Batterhead221/HIVE/Outputs/IMG/L1-SIG.png

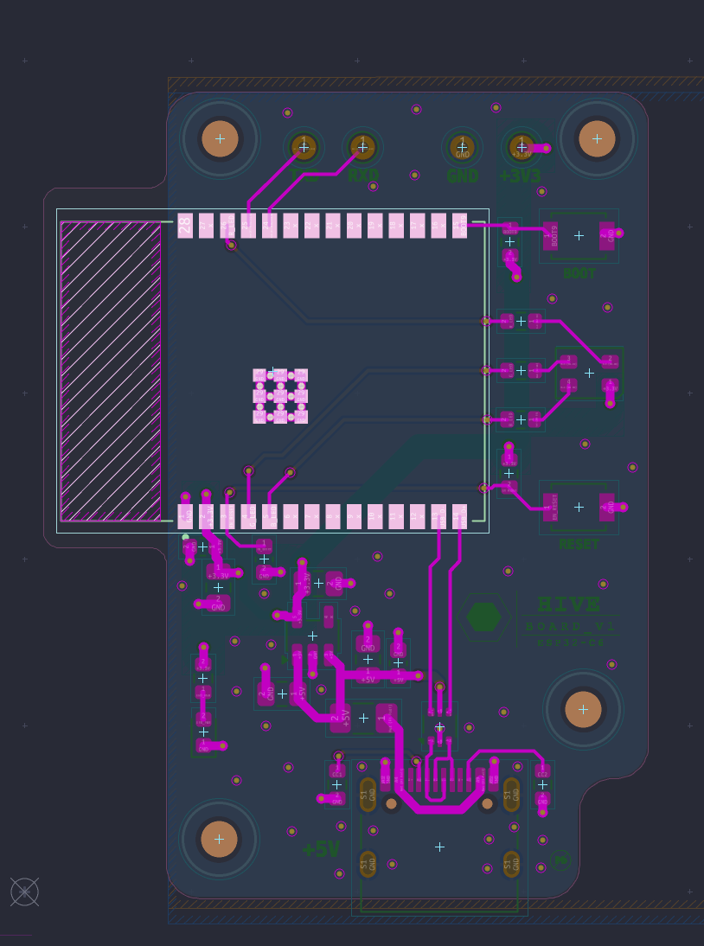
Outputs/IMG/L1-SIG.png
