Batterhead221/HIVE/Outputs/IMG/L2_GND.png

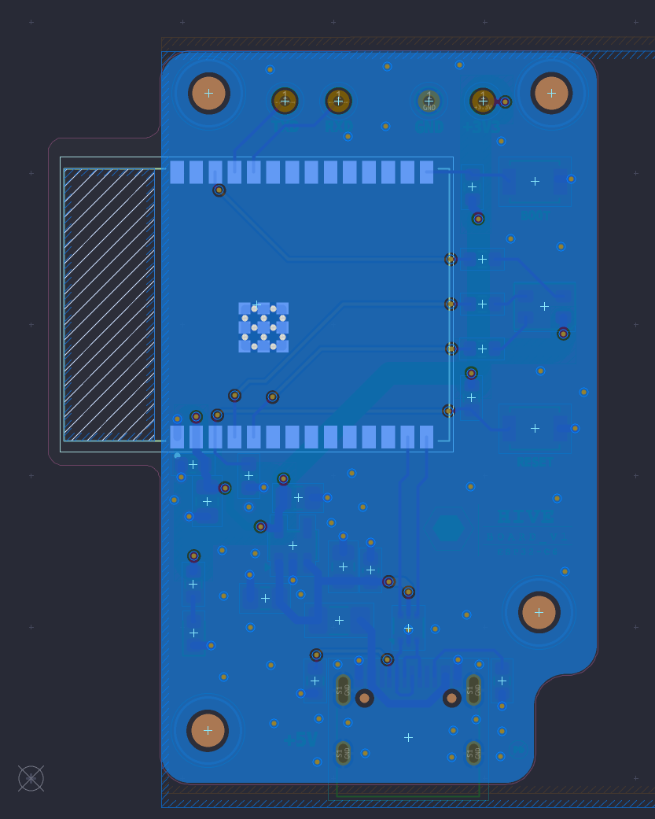
Outputs/IMG/L2_GND.png
