Batterhead221/HIVE/Outputs/IMG/L3-3V3.png

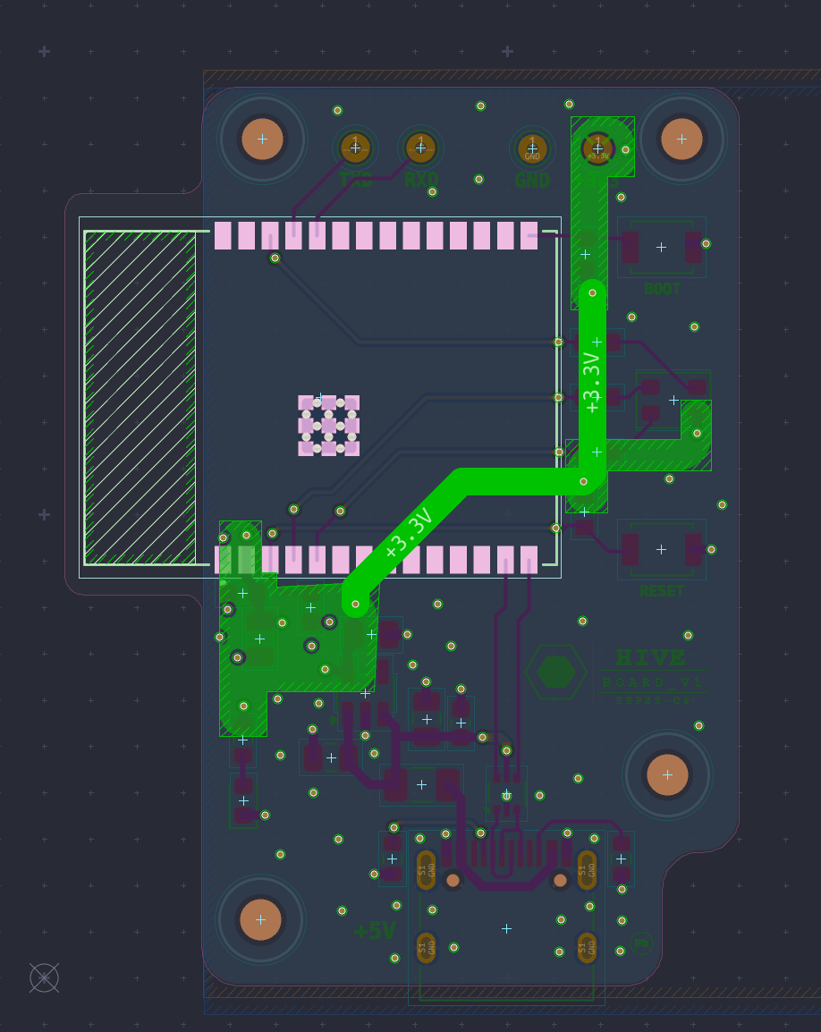
Outputs/IMG/L3-3V3.png
