Batterhead221/HIVE/Outputs/IMG/L4-MIX.png

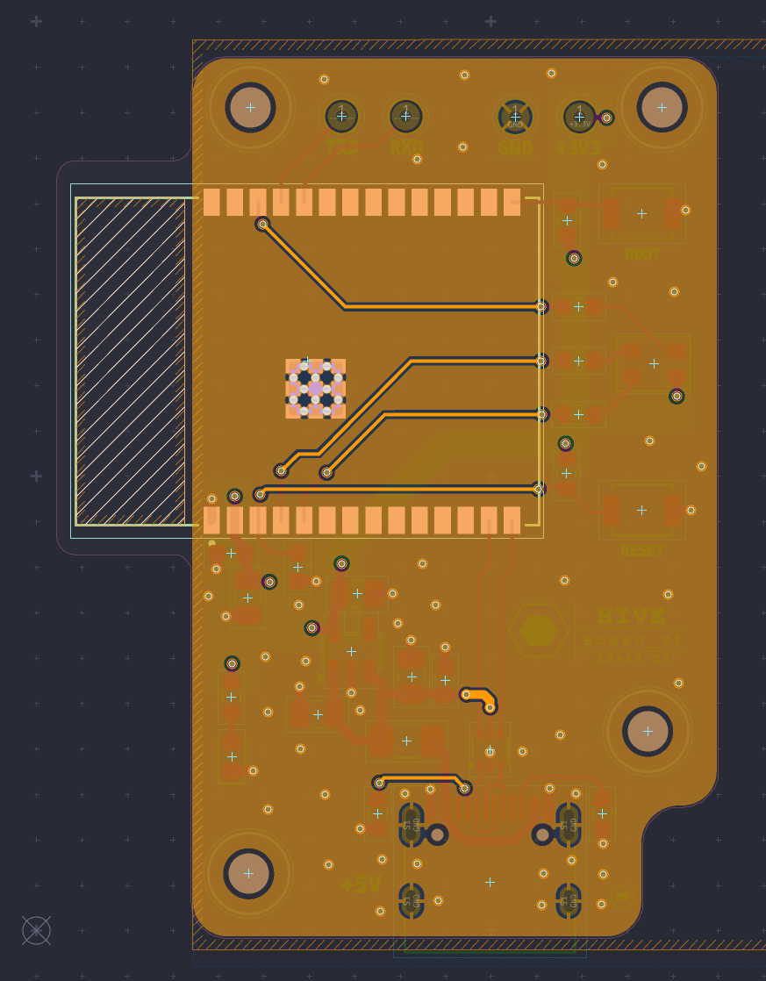
Outputs/IMG/L4-MIX.png
